borko-rajkovic/8bit-gmail-notifier/8bit-gmail-notifier/8bit-gmail-notifier/Melodies.asm

/*
 * Melodies.inc
 *
 *        Date: 09.01.2016 15:58:11
 *        Author: Borko Rajkovic
 */ 

 super_mario:

.DW 40, 0
.DW    E7, 84, P, 70, E7, 84, P, 70, P,  84, P, 70, E7, 84, P, 70
.DW    P,  84, P, 70, C7, 84, P, 70, E7, 84, P, 70, P,  84, P, 70
.DW    G7, 84, P, 70, P,  84, P, 70, P,  84, P, 70, P,  84, P, 70
.DW    G6, 84, P, 70, P,  84, P, 70, P,  84, P, 70, P,  84, P, 70

; Uncomment lines bellow to include full melody for Super Mario

/*

.DW    C7, 8, P, 12, P,    8, P, 12, P,  8, P, 12, G6, 8, P, 12,
.DW    P,  8, P, 12, P,    8, P, 12, E6, 8, P, 12, P,  8, P, 12,
.DW    P,  8, P, 12, A6,   8, P, 12, P,  8, P, 12, B6, 8, P, 12,
.DW    P,  8, P, 12, Ais6, 8, P, 12, A6, 8, P, 12, P,  8, P, 12,

.DW    G6, 8, P, 12, E7,   8, P, 12, G7, 8, P, 12,
.DW    A7, 8, P, 12, P,    8, P, 12, F7, 8, P, 12, G7, 8, P, 12,
.DW    P,  8, P, 12, E7,   8, P, 12, P,  8, P, 12, C7, 8, P, 12,
.DW    D7, 8, P, 12, B6,   8, P, 12, P,  8, P, 12, P,  8, P, 12,

.DW    C7, 8, P, 12, P,    8, P, 12, P,  8, P, 12, G6, 8, P, 12,
.DW    P,  8, P, 12, P,    8, P, 12, E6, 8, P, 12, P,  8, P, 12,
.DW    P,  8, P, 12, A6,   8, P, 12, P,  8, P, 12, B6, 8, P, 12,
.DW    P,  8, P, 12, Ais6, 8, P, 12, A6, 8, P, 12, P,  8, P, 12,

.DW    G6, 8, P, 12, E7,   8, P, 12, G7, 8, P, 12,
.DW    A7, 8, P, 12, P,    8, P, 12, F7, 8, P, 12, G7, 8, P, 12,
.DW    P,  8, P, 12, E7,   8, P, 12, P,  8, P, 12, C7, 8, P, 12,
.DW    D7, 8, P, 12, B6,   8, P, 12, P,  8, P, 12, P,  8, P, 12,

*/

.DW 0, 0

starwars:

.DW 150,  0
.DW Ais2, 175, Ais2, 175, P,    115, F3, 175, F3,   175, P, 115, Dis3, 115, P, 115, D3, 115, P,  115, C3,   115, P,    115, Ais3, 175
.DW Ais3, 175, P,    115, F3,   175, P,  115, Dis3, 115, P, 115, D3,   115, P, 115, C3, 115, P,  115, Ais3, 175, Ais3, 175, P,    115
.DW F3,   175, P,    115, Dis3, 115, P,  115, D3,   115, P, 115, Dis3, 115, P, 115, C3, 175, C3, 175
.DW 0, 0
